gbtsui/fortissimo-ii/3d_models/sources/PJ320A/reference picture-1.PNG

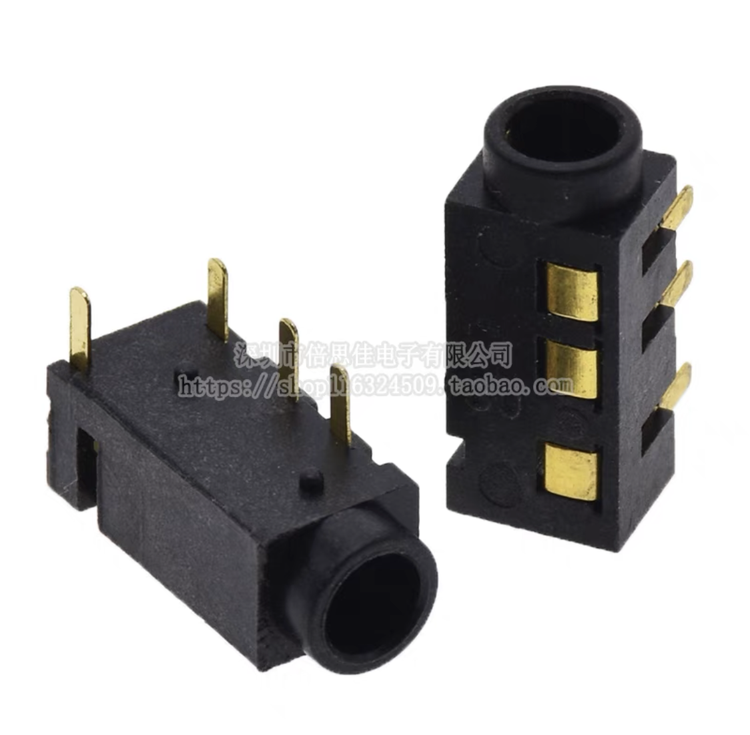
3d_models/sources/PJ320A/reference picture-1.PNG
