gbtsui/fortissimo-ii/3d_models/sources/PJ320A/reference picture-2.JPG

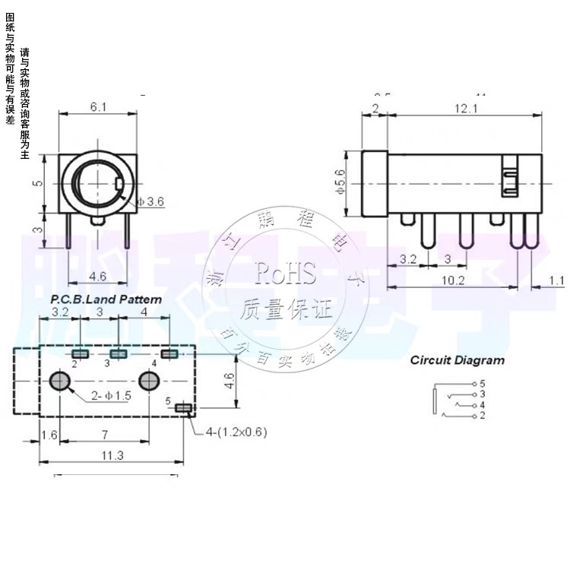
3d_models/sources/PJ320A/reference picture-2.JPG
