gbtsui/fortissimo-ii/images/renders/mrrrp.png

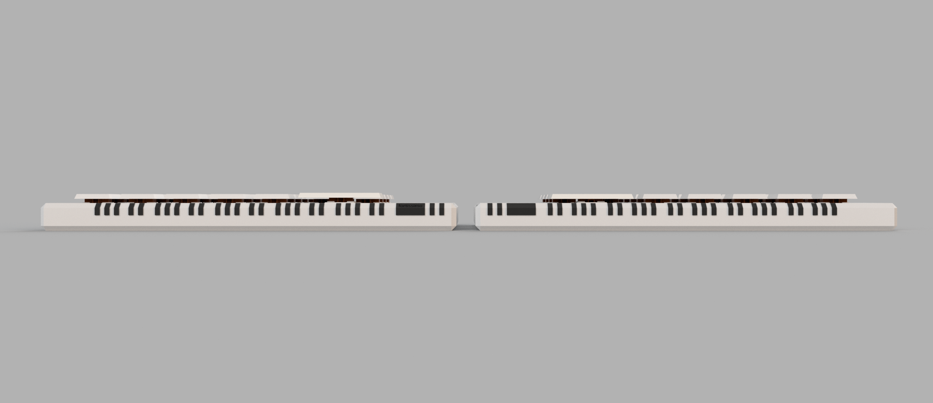
images/renders/mrrrp.png
