gbtsui/fortissimo-ii/images/renders/SHINYYYY colon three.png

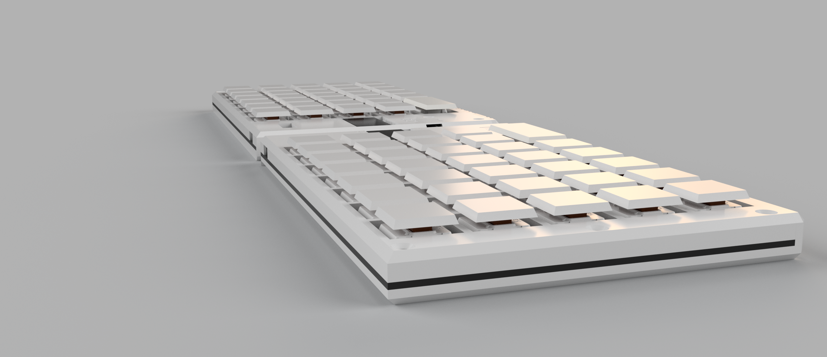
images/renders/SHINYYYY colon three.png
