gbtsui/fortissimo-ii/prod/Case Right Side Top.step

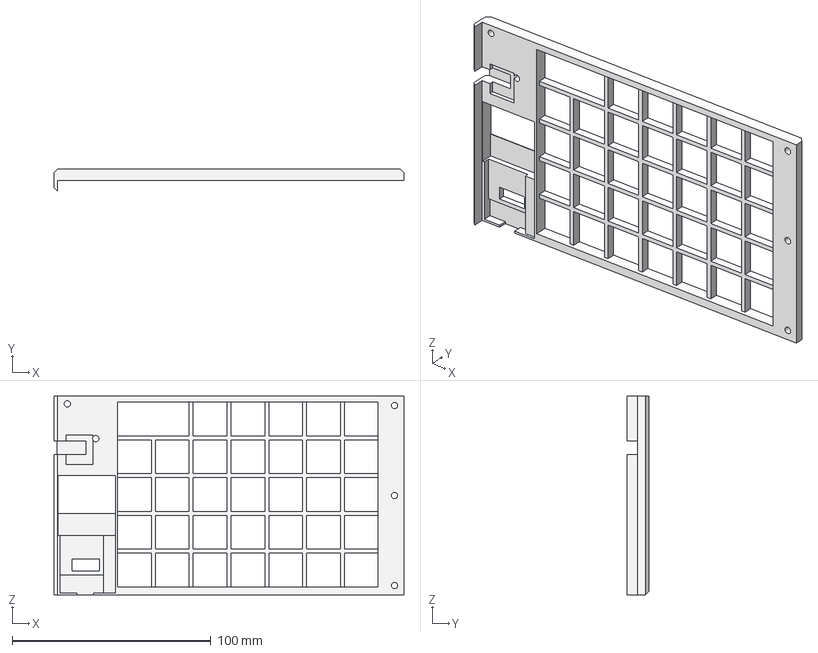
[picture p28: CAD file, 2025-08-16]
prod/Case Right Side Top.step
176.0 x 11.3 x 100.0 mm
